zdenekru/ESP32-Mark0/CodeESP32/ESP32_Mark0_Github_ready/secrets_example.h

// secrets.h
#ifndef SECRETS_H
#define SECRETS_H

// WiFi Credentials
#define WIFI_SSID       "your_wifi_name"
#define WIFI_PASSWORD   ""your_wifi_password"

// Blynk
#define BLYNK_TEMPLATE_ID           "your_template_id"
#define BLYNK_TEMPLATE_NAME         "your_template_name"
#define BLYNK_AUTH_TOKEN            "your_blynk_auth_token"

// OpenWeatherMap API
#define WEATHER_API_KEY  "your_weather_api_key"

// My local machine IP 
#define LOCAL_SERVER_URL "http://<your-pc-ip>:5000/data"  // Replace with real IP

#endif
